spyqqqdia/Knife/knives/LAV/LAV_Itm_28cm.dxf

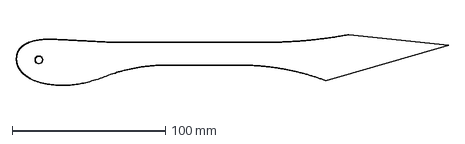
[picture p19: CAD file, 2020-10-17]
knives/LAV/LAV_Itm_28cm.dxf
281.6 x 33.1 mm
