spyqqqdia/Knife/knives/Viz/Viz_26cm_thick_2sided_A.dxf

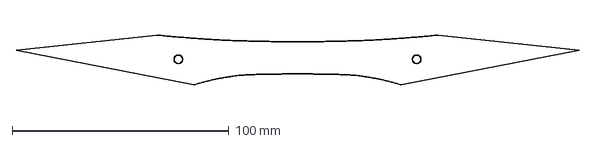
[picture p20: CAD file, 2020-11-27]
knives/Viz/Viz_26cm_thick_2sided_A.dxf
260.0 x 23.0 mm
