spyqqqdia/Knife/knives/LAV/LAV_mt_27cm.dxf

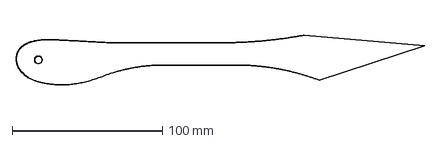
[picture p21: CAD file, 2020-10-17]
knives/LAV/LAV_mt_27cm.dxf
271.6 x 33.1 mm
