spyqqqdia/Knife/knives/Viz/Viz_26cm_thick_2sided.dxf

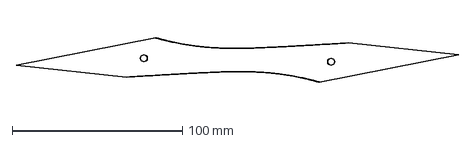
[picture p22: CAD file, 2020-11-27]
knives/Viz/Viz_26cm_thick_2sided.dxf
260.0 x 26.0 mm
