spyqqqdia/Knife/knives/LAV/LAV_lt_27cm.dxf

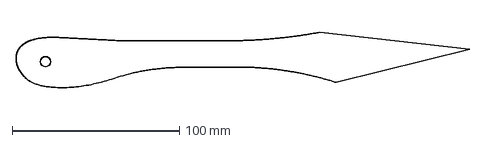
[picture p23: CAD file, 2020-10-16]
knives/LAV/LAV_lt_27cm.dxf
271.6 x 33.1 mm
