spyqqqdia/Knife/knives/Viz/Viz_25cm_thick.dxf

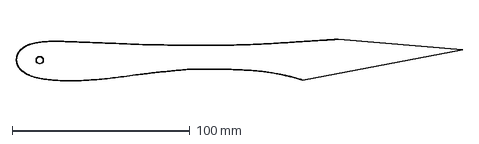
[picture p24: CAD file, 2020-11-26]
knives/Viz/Viz_25cm_thick.dxf
251.1 x 23.4 mm
