spyqqqdia/Knife/knives/LAV/LAV_st_2sided.dxf

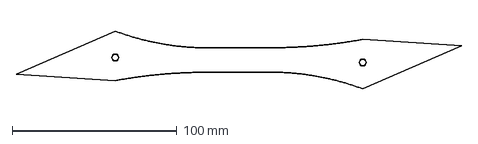
[picture p25: CAD file, 2020-10-10]
knives/LAV/LAV_st_2sided.dxf
270.0 x 35.0 mm
