spyqqqdia/Knife/knives/Viz/Viz_25cm_thick_2sided_A.dxf

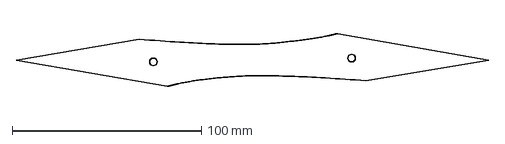
[picture p26: CAD file, 2020-11-24]
knives/Viz/Viz_25cm_thick_2sided_A.dxf
250.0 x 28.0 mm
