spyqqqdia/Knife/knives/LAV/LAV_st_26cm.dxf

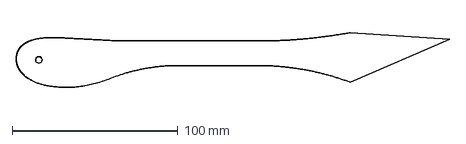
[picture p27: CAD file, 2020-10-10]
knives/LAV/LAV_st_26cm.dxf
261.6 x 33.1 mm
