spyqqqdia/Knife/knives/Viz/Viz_25cm_thick_2sided.dxf

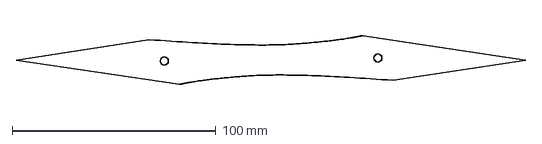
[picture p28: CAD file, 2020-11-24]
knives/Viz/Viz_25cm_thick_2sided.dxf
250.0 x 24.0 mm
