spyqqqdia/Knife/knives/LAV/LAV_st_27cm.dxf

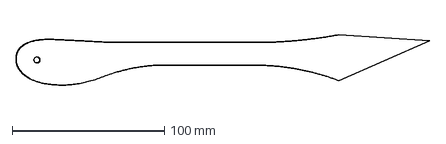
[picture p29: CAD file, 2020-10-10]
knives/LAV/LAV_st_27cm.dxf
271.6 x 33.1 mm
