spyqqqdia/Knife/knives/Viz/Viz_24cm_thick.dxf

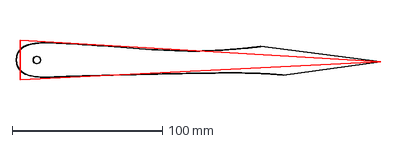
[picture p30: CAD file, 2020-11-23]
knives/Viz/Viz_24cm_thick.dxf
242.6 x 26.0 mm
