spyqqqdia/Knife/knives/Viz/Viz_27cm_6mm_2sided.dxf

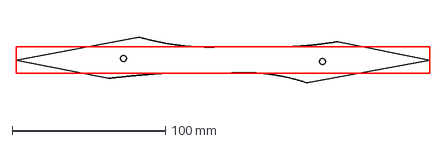
[picture p31: CAD file, 2020-11-16]
knives/Viz/Viz_27cm_6mm_2sided.dxf
270.0 x 30.0 mm
