spyqqqdia/Knife/knives/Viz/Viz_27cm_two_sided.dxf

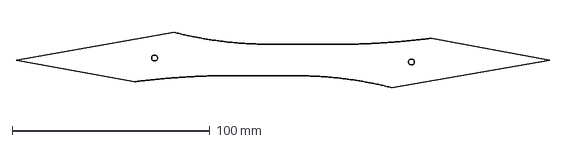
[picture p32: CAD file, 2020-11-11]
knives/Viz/Viz_27cm_two_sided.dxf
270.0 x 28.0 mm
