spyqqqdia/Knife/knives/Viz/Viz_24cm.dxf

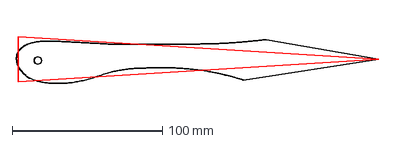
[picture p33: CAD file, 2020-11-05]
knives/Viz/Viz_24cm.dxf
241.3 x 31.3 mm
