spyqqqdia/Knife/knives/Viz/Viz1_25cm.dxf

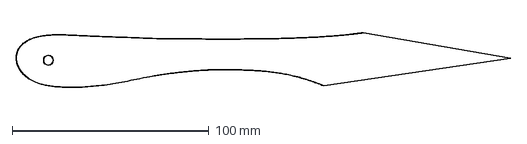
[picture p34: CAD file, 2020-11-05]
knives/Viz/Viz1_25cm.dxf
251.3 x 27.8 mm
