spyqqqdia/Knife/knives/Viz/Viz_25cm.dxf

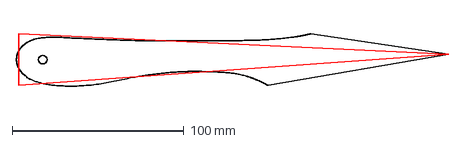
[picture p35: CAD file, 2020-11-05]
knives/Viz/Viz_25cm.dxf
251.3 x 30.5 mm
