spyqqqdia/Knife/knives/Viz/Viz_24cm.pdf

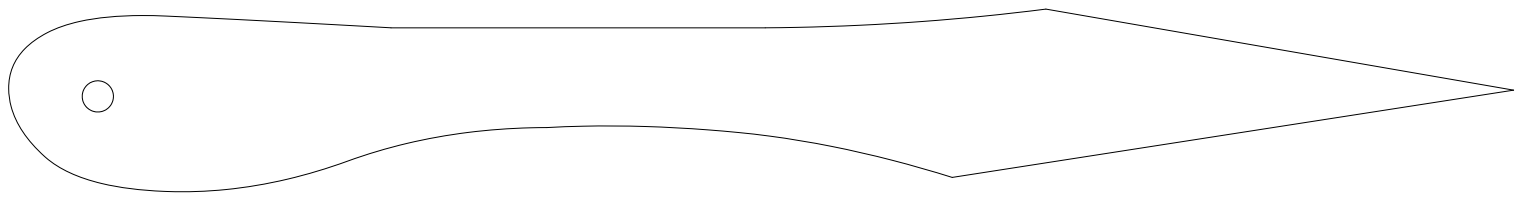
[picture p37: page 1]
