spyqqqdia/Knife/knives/Viz/Viz_25cm.pdf

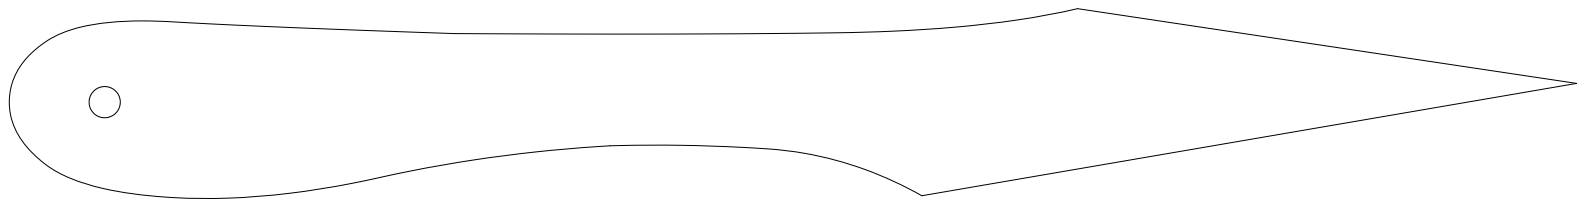
[picture p38: page 1]
