spyqqqdia/Knife/knives/LAV/LAV_ltm_28cm.pdf

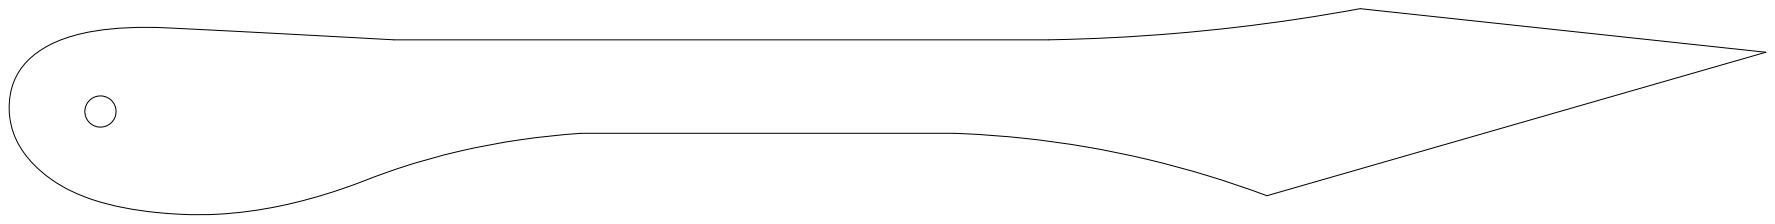
[picture p39: page 1]
