spyqqqdia/Knife/knives/LAV/LAV_mt_27cm.pdf

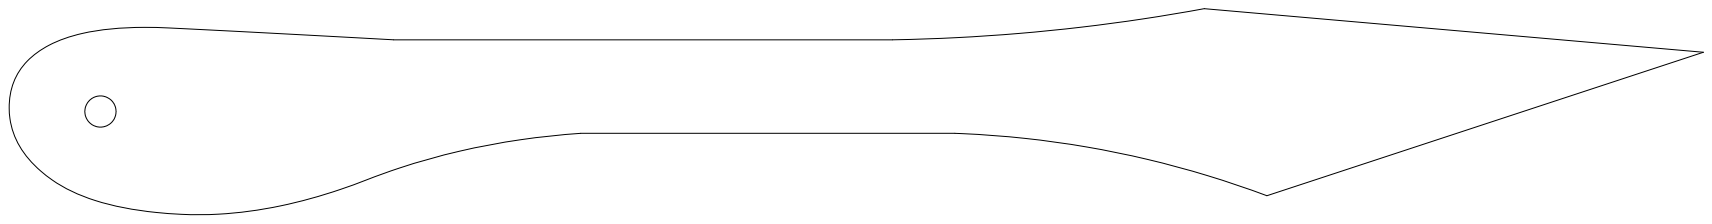
[picture p40: page 1]
