spyqqqdia/Knife/knives/LAV/LAV_lt_27cm.pdf

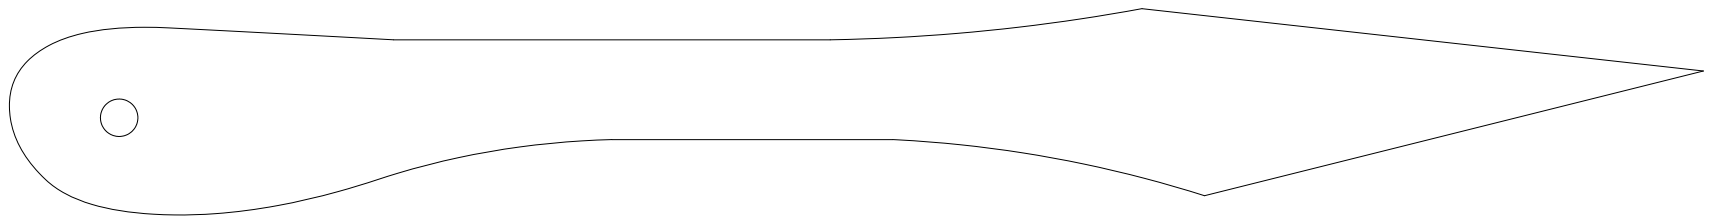
[picture p41: page 1]
