spyqqqdia/Knife/knives/LAV/LAV_st_26cm.pdf

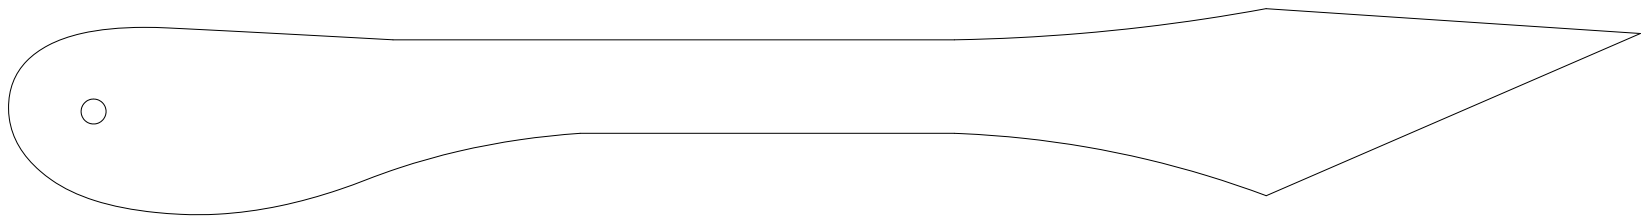
[picture p42: page 1]
