spyqqqdia/Knife/knives/LAV/LAV_st_27cm.pdf

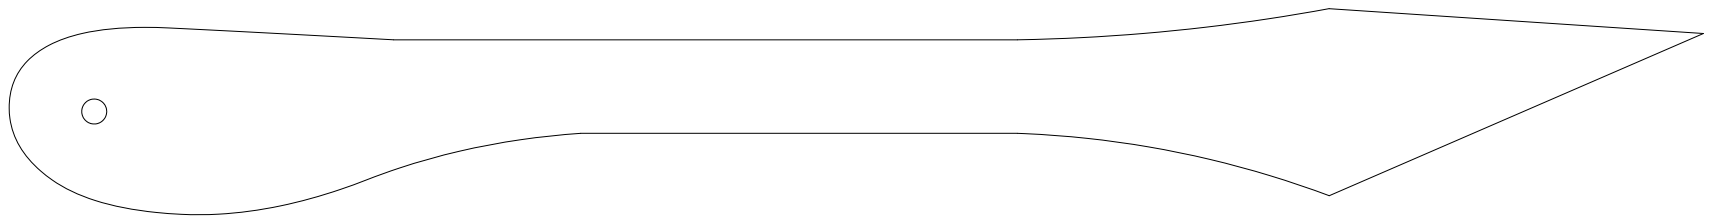
[picture p43: page 1]
