spyqqqdia/Knife/knives/LAV/LAV_st_2sided_27cm.pdf

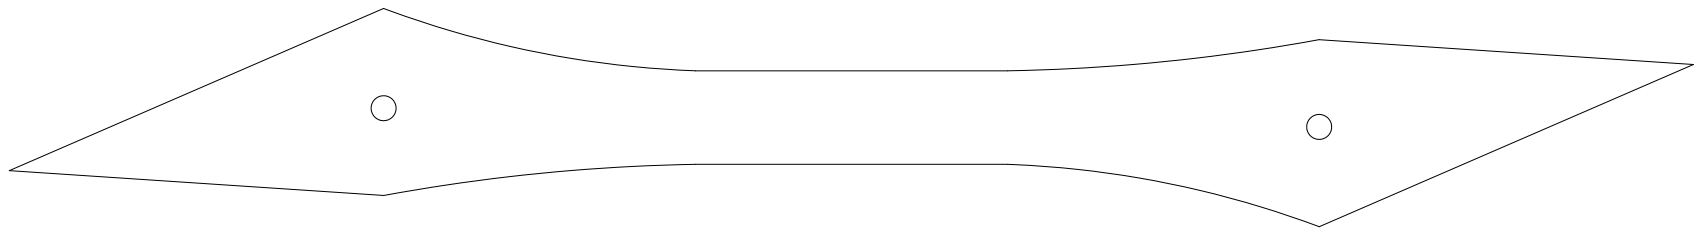
[picture p44: page 1]
